ryan-barry-99/Advanced_Robotics_Final_Project_Sp23/CAD_Files/Omni_wheel_side.SLDPRT

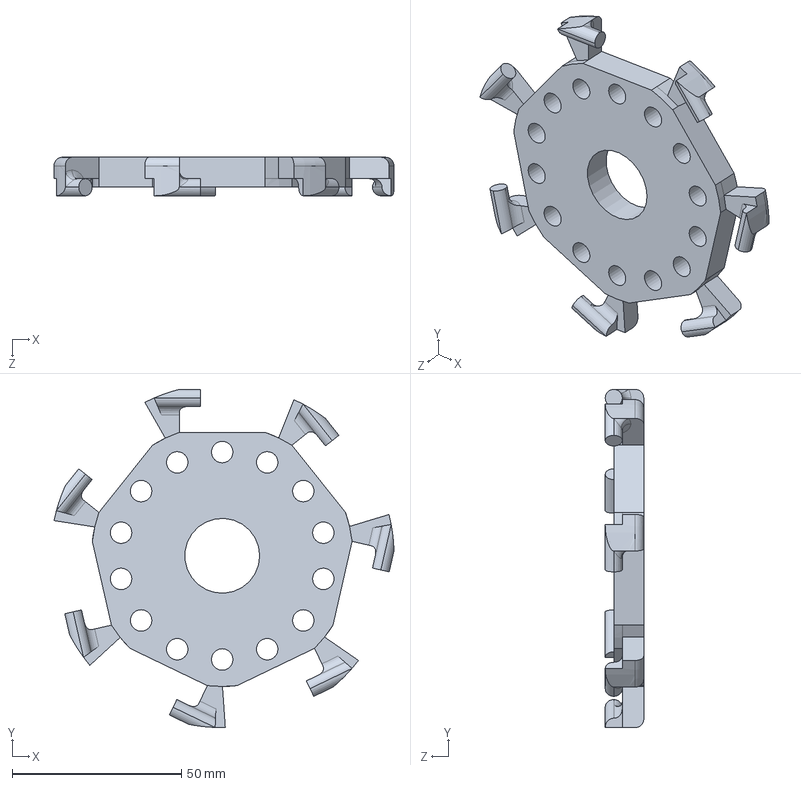
[picture p15: CAD file, 2023-03-19]
CAD_Files/Omni_wheel_side.SLDPRT
100.5 x 100.0 x 11.4 mm
