ryan-barry-99/Advanced_Robotics_Final_Project_Sp23/CAD_Files/washer.SLDPRT

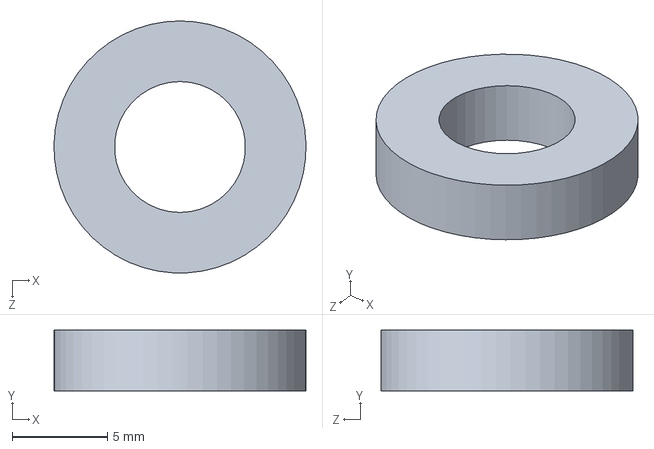
[picture p16: CAD file, 2023-03-19]
CAD_Files/washer.SLDPRT
13.2 x 3.17 x 13.2 mm
