ryan-barry-99/Advanced_Robotics_Final_Project_Sp23/Deployment/pid_controller.py

class PIDController:
    def __init__(self, kp, ki, kd):
        self.kp = kp
        self.ki = ki
        self.kd = kd
        self.integral = 0
        self.previous_error = 0

    def update(self, targeted_velocity, current_velocity):
        error = targeted_velocity - current_velocity  # 
        self.integral += error
        derivative = error - self.previous_error
        output = self.kp * error + self.ki * self.integral + self.kd * derivative
        self.previous_error = error
        return output
