ryan-barry-99/Advanced_Robotics_Final_Project_Sp23/Deployment/pinout.py

# pinout.py
# A dictionary containing the Jetson Nano GPIO pin numbers for the robot. Updating this file updates pin assignments globally

pinout = {
    'encoder_1_a': 11,
    'encoder_1_b': 12,
    'encoder_2_a': 15,
    'encoder_2_b': 16,
    'encoder_3_a': 18,
    'encoder_3_b': 19,
    'motor_1_dir_a': 21,
    'motor_1_dir_b': 22,
    'motor_1_pwm': 23,
    'motor_2_dir_a': 24,
    'motor_2_dir_b': 26,
    'motor_2_pwm': 29,
    'motor_3_dir_a': 31,
    'motor_3_dir_b': 33,
    'motor_3_pwm': 35
}
